MichaelThessel/arduino-stoerbert/commands.h

#ifndef COMMANDS_H
#define COMMANDS_H

// Command to character mappings
const char COMMAND0                 = '0';
const char COMMAND1                 = '1';
const char COMMAND2                 = '2';
const char COMMAND3                 = '3';
const char COMMAND4                 = '4';
const char COMMAND5                 = '5';
const char COMMAND6                 = '6';
const char COMMAND7                 = '7';
const char COMMAND8                 = '8';
const char COMMAND9                 = '9';
const char COMMAND_PLAY_PAUSE       = 'p';
const char COMMAND_PREVIOUS         = 'b';
const char COMMAND_NEXT             = 'f';
const char COMMAND_GOD_MODE         = 'g';
const char COMMAND_INCREASE_VOLUME  = '+';
const char COMMAND_DECREASE_VOLUME  = '-';

#endif
